goonmandu/GoonBoard-HE/include/Descriptors.h

/*
             LUFA Library
     Copyright (C) Dean Camera, 2021.

  dean [at] fourwalledcubicle [dot] com
           www.lufa-lib.org
*/

/*
  Copyright 2021  Dean Camera (dean [at] fourwalledcubicle [dot] com)

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
  The author disclaims all warranties with regard to this
  software, including all implied warranties of merchantability
  and fitness.  In no event shall the author be liable for any
  special, indirect or consequential damages or any damages
  whatsoever resulting from loss of use, data or profits, whether
  in an action of contract, negligence or other tortious action,
  arising out of or in connection with the use or performance of
  this software.
*/

/** \file
 *
 *  Header file for Descriptors.c.
 */

#ifndef _DESCRIPTORS_H_
#define _DESCRIPTORS_H_

    /* Includes: */
        #include <avr/pgmspace.h>
        #include "../lib/LUFA/Drivers/USB/USB.h"
        #include "KeyboardConfig.h"

    /* Type Defines: */
        /** Type define for the device configuration descriptor structure. This must be defined in the
         *  application code, as the configuration descriptor contains several sub-descriptors which
         *  vary between devices, and which describe the device's usage to the host.
         */
        typedef struct
        {
            USB_Descriptor_Configuration_Header_t Config;

            // Keyboard HID Interface
            USB_Descriptor_Interface_t              HID_Interface;
            USB_HID_Descriptor_HID_t                HID_KeyboardHID;
            USB_Descriptor_Endpoint_t               HID_ReportINEndpoint;
            
            // RawHID Interface
            USB_Descriptor_Interface_t              RawHID_Interface;
            USB_HID_Descriptor_HID_t                RawHID_RawHID;
            USB_Descriptor_Endpoint_t               RawHID_ReportINEndpoint;
        } USB_Descriptor_Configuration_t;

        /** Enum for the device interface descriptor IDs within the device. Each interface descriptor
         *  should have a unique ID index associated with it, which can be used to refer to the
         *  interface from other descriptors.
         */
        enum InterfaceDescriptors_t
        {
            INTERFACE_ID_Keyboard       = 0, /**< Keyboard interface descriptor ID */
            INTERFACE_ID_RawHID         = 1, /**< RawHID interface descriptor ID */
        };

        /** Enum for the device string descriptor IDs within the device. Each string descriptor should
         *  have a unique ID index associated with it, which can be used to refer to the string from
         *  other descriptors.
         */
        enum StringDescriptors_t
        {
            STRING_ID_Language     = 0, /**< Supported Languages string descriptor ID (must be zero) */
            STRING_ID_Manufacturer = 1, /**< Manufacturer string ID */
            STRING_ID_Product      = 2, /**< Product string ID */
        };

    /* Macros: */
        /** Endpoint address of the Keyboard HID reporting IN endpoint. */
        #define KEYBOARD_EPADDR                 (ENDPOINT_DIR_IN | 1)

        /** Endpoint addresses of the RawHID interface. */
        #define RAWHID_IN_EPADDR                (ENDPOINT_DIR_IN | 2)
        #define RAWHID_OUT_EPADDR               (ENDPOINT_DIR_OUT | 3)  // Unused

/** Size in bytes of the endpoints. */
#define KEYBOARD_EPSIZE                 (64)
#define RAWHID_IN_EPSIZE                (64)
#define RAWHID_OUT_EPSIZE               (64)

    /* Report ID/Command ID Codes */
        /** Keyboard Lock LEDs Request is the same as Keyboard HID ReportID */
        #define LOCK_LEDS_REPORT_ID                 HID_KEYBOARD_REPORT_ID

        #define BASIC_KEYCODES_REPORT_ID            0x01
        #define CONSUMER_CONTROLS_REPORT_ID         0x02

        /** Fetch Configuration Request */
        #define FETCH_CONFIG_REPORT_ID              0xC0
        #define FETCH_CONFIG_REPORT_SIZE            204  /** sizeof(default_settings) */ 

        /** On-the-fly Edit Request IDs */
        #define CUSTOM_COMMAND_REPORT_ID            0xFE

        #define EDIT_KEYMAP_COMMAND_ID              0xA0
        #define EDIT_KEYMAP_COMMAND_BYTES           4

        #define EDIT_ACTUATIONS_COMMAND_ID          0xA1
        #define EDIT_ACTUATIONS_COMMAND_BYTES       4

        #define EDIT_ROTARY_KEYMAP_COMMAND_ID       0xA2
        #define EDIT_ROTARY_KEYMAP_COMMAND_BYTES    4

        #define EDIT_SNAPTAP_A_COMMAND_ID           0xB0
        #define EDIT_SNAPTAP_B_COMMAND_ID           0xB1
        #define EDIT_SNAPTAP_COMMAND_BYTES          4

        #define EDIT_RAPID_TRIGGER_COMMAND_ID       0xD0
        #define EDIT_RAPID_TRIGGER_COMMAND_BYTES    4


    /* Function Prototypes: */
    /*
        uint16_t CALLBACK_USB_GetDescriptor(const uint16_t wValue,
                                            const uint16_t wIndex,
                                            const void** const DescriptorAddress)
                                            ATTR_WARN_UNUSED_RESULT ATTR_NON_NULL_PTR_ARG(3);
     */

#endif
