goonmandu/GoonBoard-HE/src/SnapTap.c

#include "SnapTap.h"
#include "KeyboardConfig.h"
#include "MatrixScanner.h"

/**
 * To be called immediately after finalized Keyboard Report generation.
 * 
 * This is the specific SOCD variety: Key-Agnostic Last-In aka "SnapTap" by Razer.
 * Let's say we have them mapped to A and D.
 * 1.   Idle.
 * 2.   A is pressed:
 *          register A as PRESSED (e.g. do nothing).
 * 3.   While A is held down, D is pressed:
 *          register A as RELEASED (update key_status) and register key 2 as PRESSED (do nothing).
 * 4.   If D is released:
 *          register A as PRESSED (do nothing)
 * 5.   If A is released:
 *          (do nothing)
 * 6.   Repeat
 * 
 * This also returns the pointer to the `key_status` matrix to restore the overridden key
 * for Rapid Trigger compatibility issues as Rapid Trigger assumes `key_status` doesn't change
 * outside of `MatrixScanner::scan_keys`.
 * 
 * If SnapTap didn't trigger, it returns 0xFFFF.
 */
uint8_t snaptap(uint8_t snaptap_module, uint8_t** ptr_to_restore) {
    static uint8_t first_key_a;
    static uint8_t first_key_b;

    switch (snaptap_module) {
        case SNAPTAP_MODULE_A:
            // SnapTap initialization, record first keypress
            if (PRESSED == key_status[ROWOF(SNAPTAP_A_KEY1_COORDS)][KEYOF(SNAPTAP_A_KEY1_COORDS)]
                && RELEASED == key_status[ROWOF(SNAPTAP_A_KEY2_COORDS)][KEYOF(SNAPTAP_A_KEY2_COORDS)]) {
                first_key_a = SNAPTAP_A_KEY1_COORDS;
                return 0;
            }
            else if (RELEASED == key_status[ROWOF(SNAPTAP_A_KEY1_COORDS)][KEYOF(SNAPTAP_A_KEY1_COORDS)]
                    && PRESSED == key_status[ROWOF(SNAPTAP_A_KEY2_COORDS)][KEYOF(SNAPTAP_A_KEY2_COORDS)]) {
                first_key_a = SNAPTAP_A_KEY2_COORDS;
                return 0;
            }

            // If both are now pressed down, cancel the first keypress
            else if (PRESSED == key_status[ROWOF(SNAPTAP_A_KEY1_COORDS)][KEYOF(SNAPTAP_A_KEY1_COORDS)]
                    && PRESSED == key_status[ROWOF(SNAPTAP_A_KEY2_COORDS)][KEYOF(SNAPTAP_A_KEY2_COORDS)]) {
                // Simultaneous press: SnapTap does nothing
                if (first_key_a == 0xFF) return 0;
                key_status[ROWOF(first_key_a)][KEYOF(first_key_a)] = 0;
                *ptr_to_restore = (uint8_t*)&key_status[ROWOF(first_key_a)][KEYOF(first_key_a)];
                return 1;
            }
            // This branch is to mark first_key as stale the USB frame immediately after
            // both keys were released so that SnapTap doesn't filter out simlutaneous
            // presses randomly
            else {
                first_key_a = 0xFF;
                return 0;
            }
            break;

        case SNAPTAP_MODULE_B:
            // SnapTap initialization, record first keypress
            if (PRESSED == key_status[ROWOF(SNAPTAP_B_KEY1_COORDS)][KEYOF(SNAPTAP_B_KEY1_COORDS)]
                && RELEASED == key_status[ROWOF(SNAPTAP_B_KEY2_COORDS)][KEYOF(SNAPTAP_B_KEY2_COORDS)]) {
                first_key_b = SNAPTAP_B_KEY1_COORDS;
                return 0;
            }
            else if (RELEASED == key_status[ROWOF(SNAPTAP_B_KEY1_COORDS)][KEYOF(SNAPTAP_B_KEY1_COORDS)]
                    && PRESSED == key_status[ROWOF(SNAPTAP_B_KEY2_COORDS)][KEYOF(SNAPTAP_B_KEY2_COORDS)]) {
                first_key_b = SNAPTAP_B_KEY2_COORDS;
                return 0;
            }

            // If both are now pressed down, cancel the first keypress
            else if (PRESSED == key_status[ROWOF(SNAPTAP_B_KEY1_COORDS)][KEYOF(SNAPTAP_B_KEY1_COORDS)]
                    && PRESSED == key_status[ROWOF(SNAPTAP_B_KEY2_COORDS)][KEYOF(SNAPTAP_B_KEY2_COORDS)]) {
                // Simultaneous press: SnapTap does nothing
                if (first_key_b == 0xFF) return 0;
                key_status[ROWOF(first_key_b)][KEYOF(first_key_b)] = 0;
                *ptr_to_restore = (uint8_t*)&key_status[ROWOF(first_key_b)][KEYOF(first_key_b)];
                return 1;
            }
            // This branch is to mark first_key as stale the USB frame immediately after
            // both keys were released so that SnapTap doesn't filter out simlutaneous
            // presses randomly
            else {
                first_key_b = 0xFF;
                return 0;
            }
            break;

        default:
            return 0;
    }
}
